RwHexa/NetzgeraetRw/AEQ/PlatineAEQ.jpg

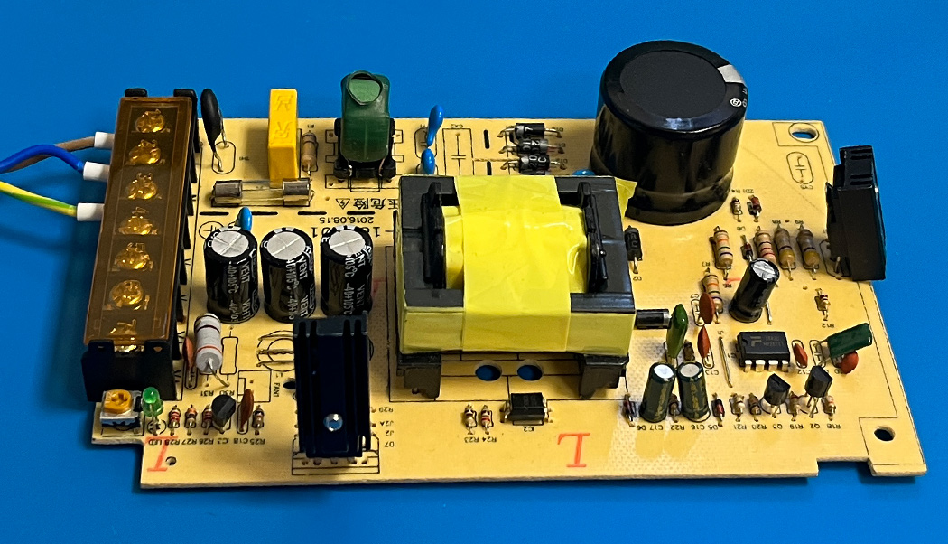
AEQ/PlatineAEQ.jpg
