RwHexa/NetzgeraetRw/AEQ/Schaltplan_Schaltnetzteil-AEQ.png

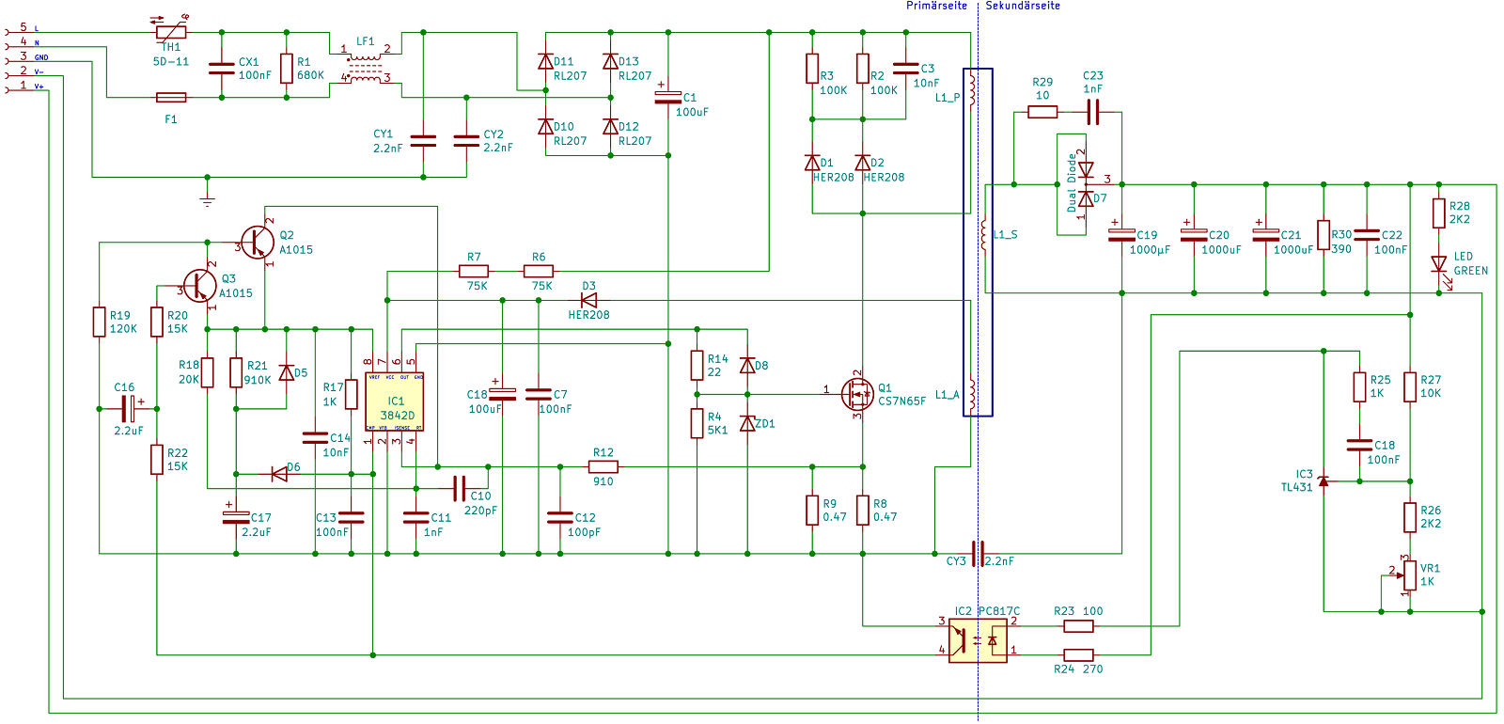
AEQ/Schaltplan_Schaltnetzteil-AEQ.png
