RwHexa/NetzgeraetRw/kicad/PlatineNetz/PlatineNetz.png

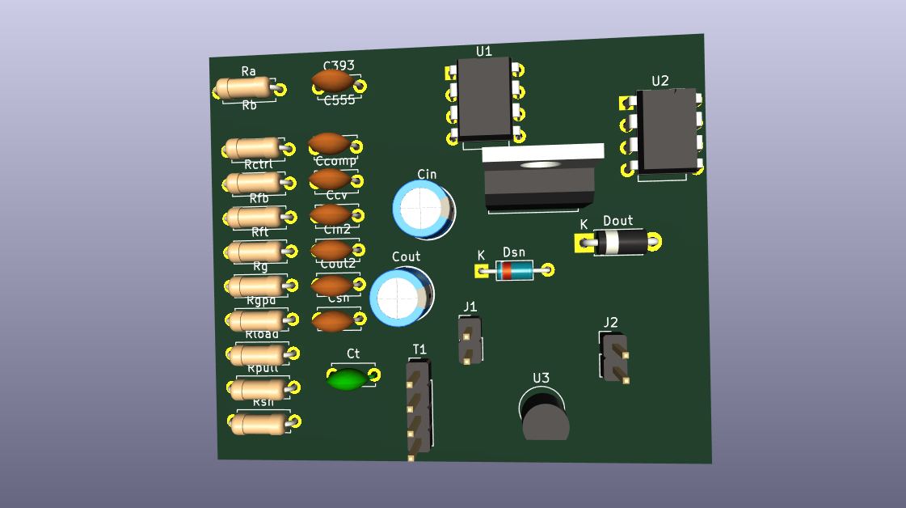
kicad/PlatineNetz/PlatineNetz.png
