RwHexa/NetzgeraetRw/Netzgerät Heft.png

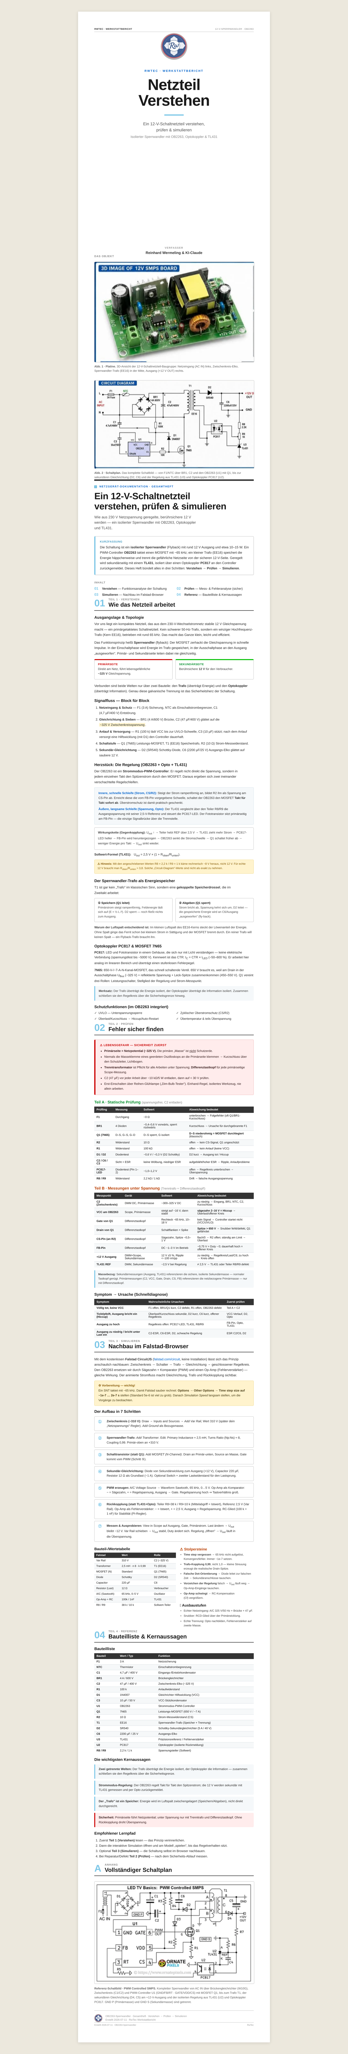
Netzgerät Heft.png
